dj1yr/LJ-RF-Powermeter-Teensy-4.1/Case/Case 5"/Powermeter compl 5Zoll_h.png

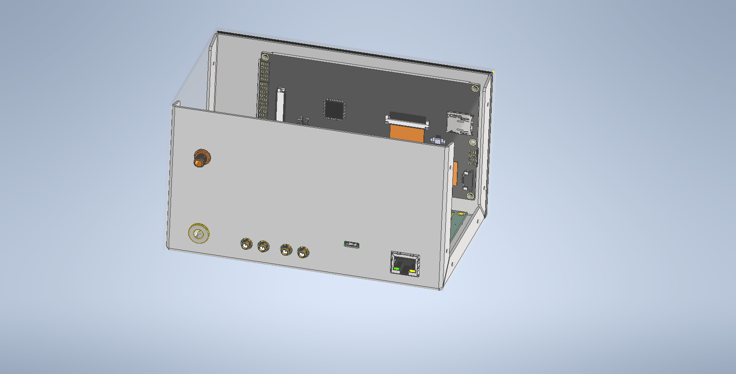
Case/Case 5"/Powermeter compl 5Zoll_h.png
