dj1yr/LJ-RF-Powermeter-Teensy-4.1/Case/RF-Coupler/RF Coupler HF-6m.png

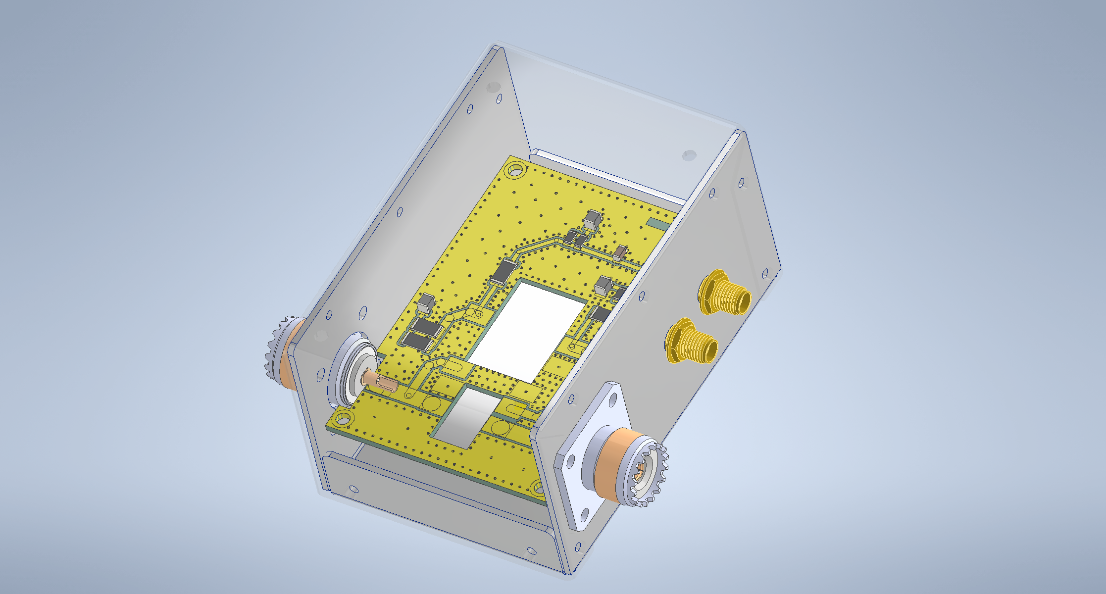
Case/RF-Coupler/RF Coupler HF-6m.png
