dj1yr/LJ-RF-Powermeter-Teensy-4.1/REV3n/extender_REV3n/extender HMC/HMC849_isolate_50khzto4Ghz.png

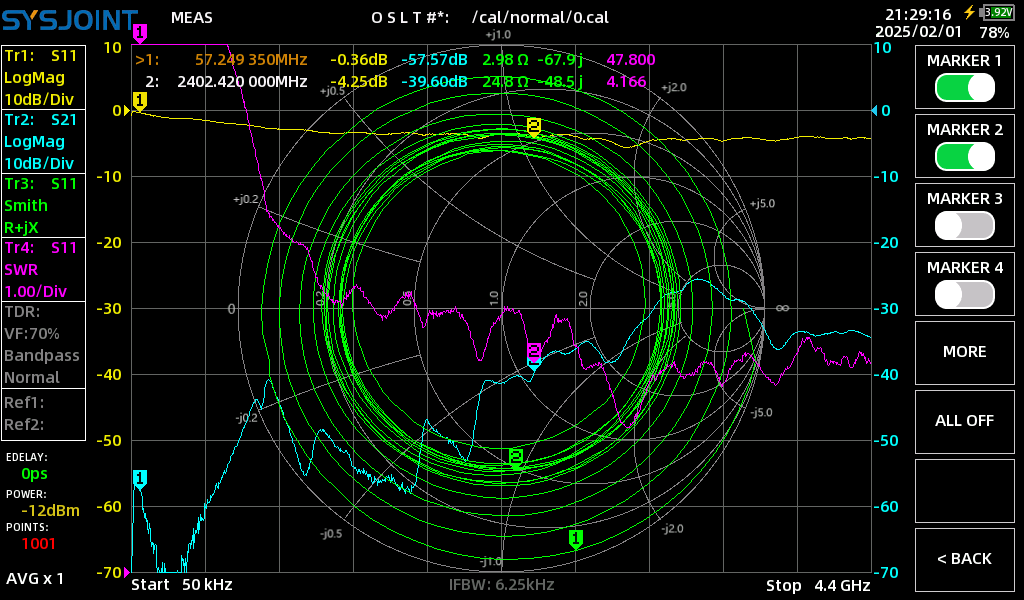
REV3n/extender_REV3n/extender HMC/HMC849_isolate_50khzto4Ghz.png
