dj1yr/LJ-RF-Powermeter-Teensy-4.1/REV3n/extender_REV3n/extender HMC/HMC849_S21_S11_1Mhzto30Mhz.png

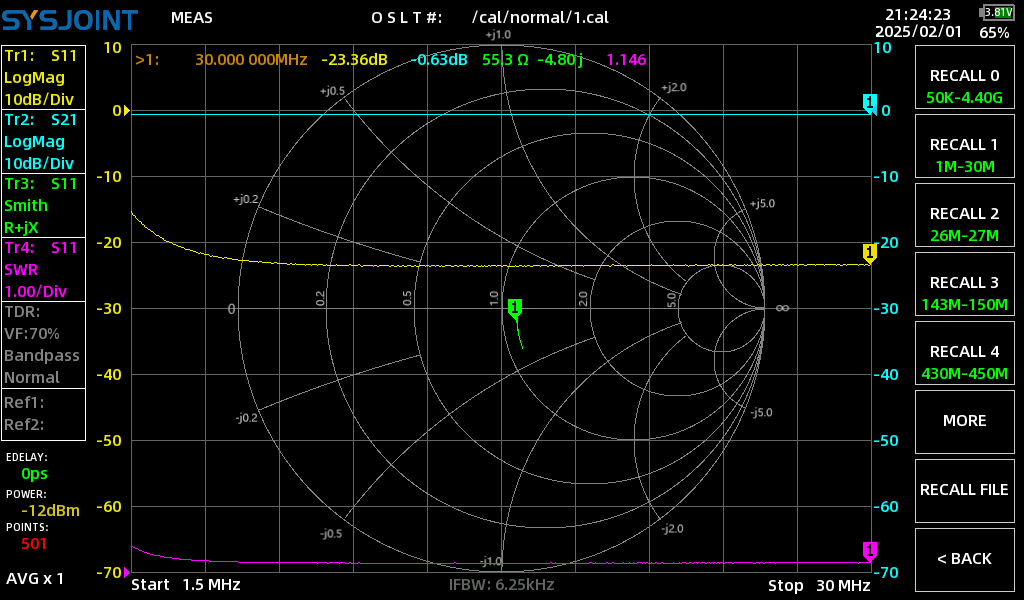
REV3n/extender_REV3n/extender HMC/HMC849_S21_S11_1Mhzto30Mhz.png
