dj1yr/LJ-RF-Powermeter-Teensy-4.1/REV3n/extender_REV3n/extender HMC/PowerMeter_REV37_2in_HMC_extender-top.png

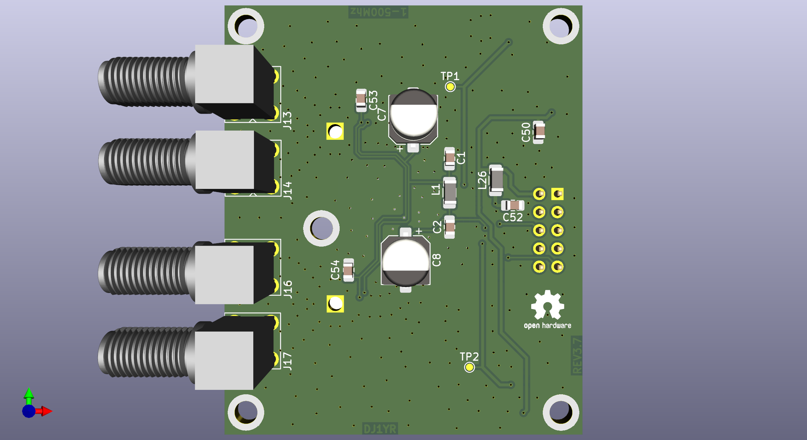
REV3n/extender_REV3n/extender HMC/PowerMeter_REV37_2in_HMC_extender-top.png
