dj1yr/LJ-RF-Powermeter-Teensy-4.1/REV3n/mainboard_REV3n/PowerMeter_REV36_top.png

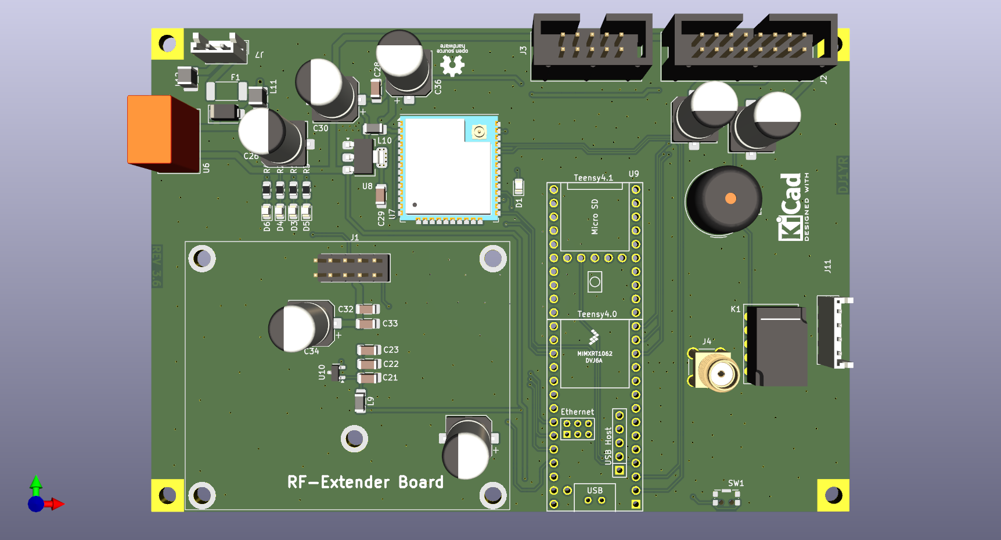
REV3n/mainboard_REV3n/PowerMeter_REV36_top.png
