dj1yr/LJ-RF-Powermeter-Teensy-4.1/RF-Coupler/RF-Coupler HF-6m/PowerMeter_REV3n_RF_coupler_top.png

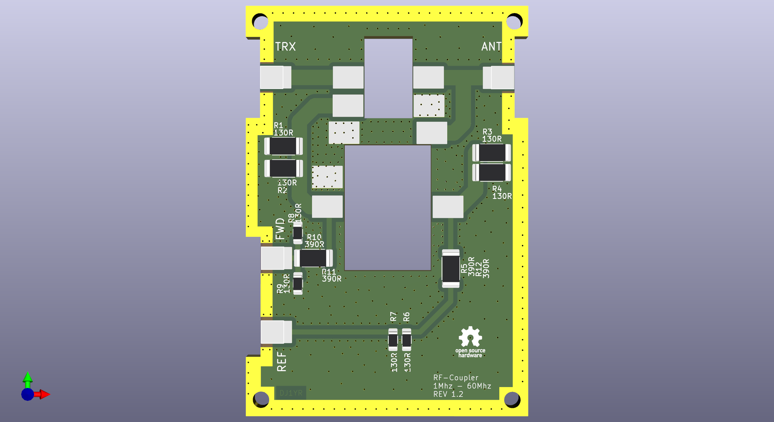
RF-Coupler/RF-Coupler HF-6m/PowerMeter_REV3n_RF_coupler_top.png
